LasiduDilshan/BMS_EDR_project/Solidworks/SW CONTROLLER/controller/Screenshot 2024-05-13 174024.png

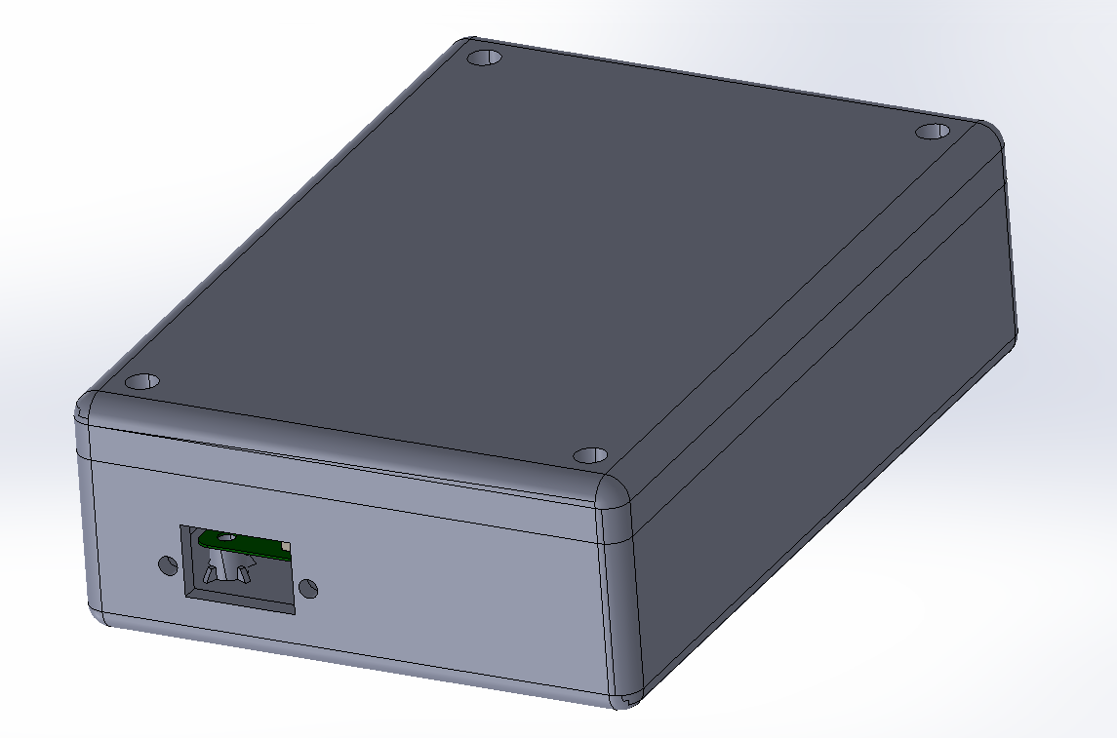
Solidworks/SW CONTROLLER/controller/Screenshot 2024-05-13 174024.png
