LasiduDilshan/BMS_EDR_project/Solidworks/SW CONTROLLER/controller/Screenshot 2024-05-13 174057.png

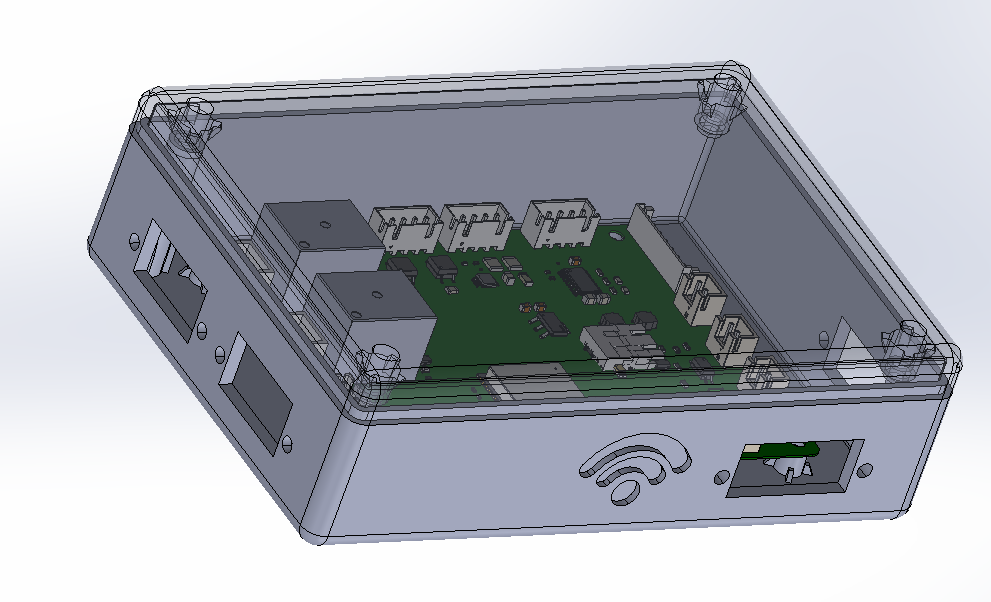
Solidworks/SW CONTROLLER/controller/Screenshot 2024-05-13 174057.png
