LasiduDilshan/BMS_EDR_project/Solidworks/SW CONTROLLER/controller/Screenshot 2024-05-13 174107.png

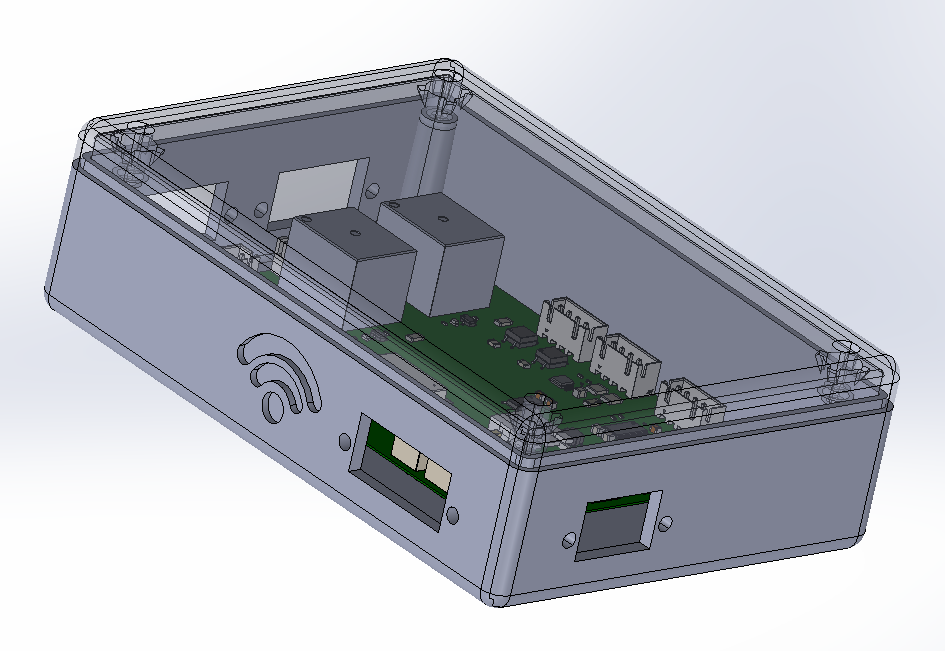
Solidworks/SW CONTROLLER/controller/Screenshot 2024-05-13 174107.png
