LasiduDilshan/BMS_EDR_project/Solidworks/SW/cell module/Screenshot 2024-05-13 142049.png

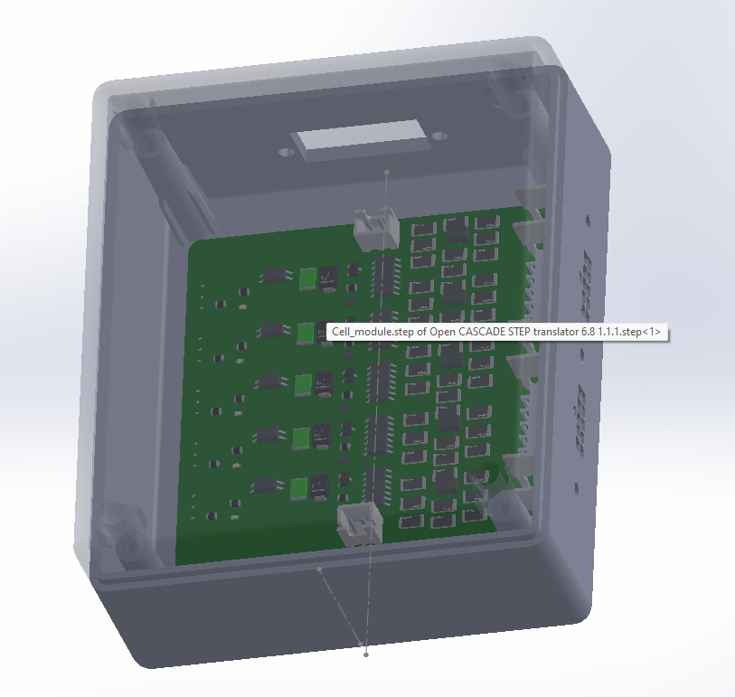
Solidworks/SW/cell module/Screenshot 2024-05-13 142049.png
