LasiduDilshan/BMS_EDR_project/PCBs/Cell Module/__Final cell module__/PCB with side mounts new.step

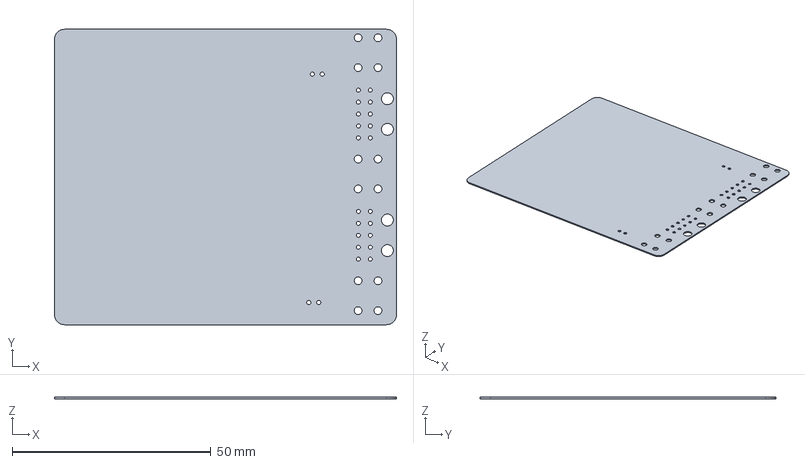
[picture p76: CAD file, 2024-07-03]
PCBs/Cell Module/__Final cell module__/PCB with side mounts new.step
86.0 x 74.3 x 0.411 mm
