LasiduDilshan/BMS_EDR_project/PCBs/Reference/BMS-Cell-Module-Circuit/DO-221AC.stp

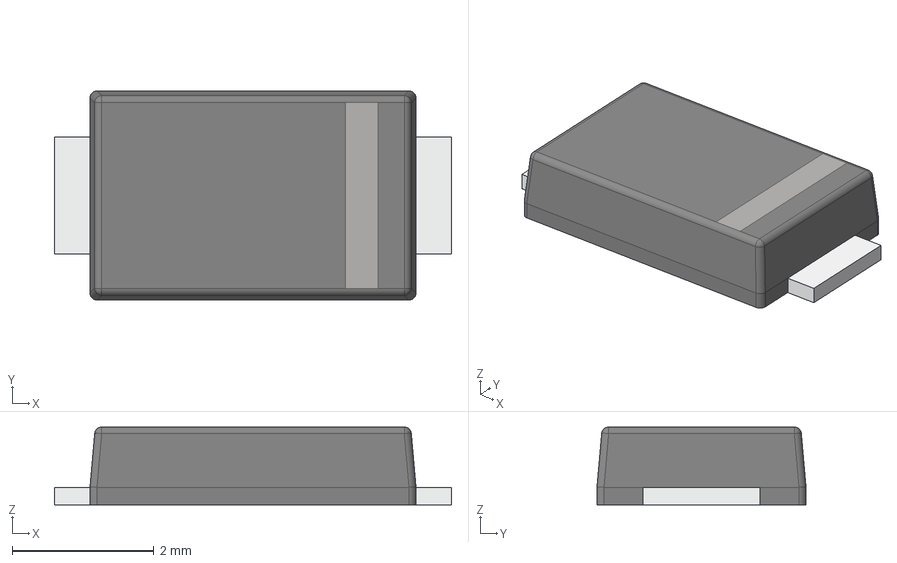
[picture p77: CAD file, 2024-07-03]
PCBs/Reference/BMS-Cell-Module-Circuit/DO-221AC.stp
5.60 x 2.95 x 1.10 mm
