LasiduDilshan/BMS_EDR_project/Solidworks/SW CONTROLLER/2nd below.SLDPRT

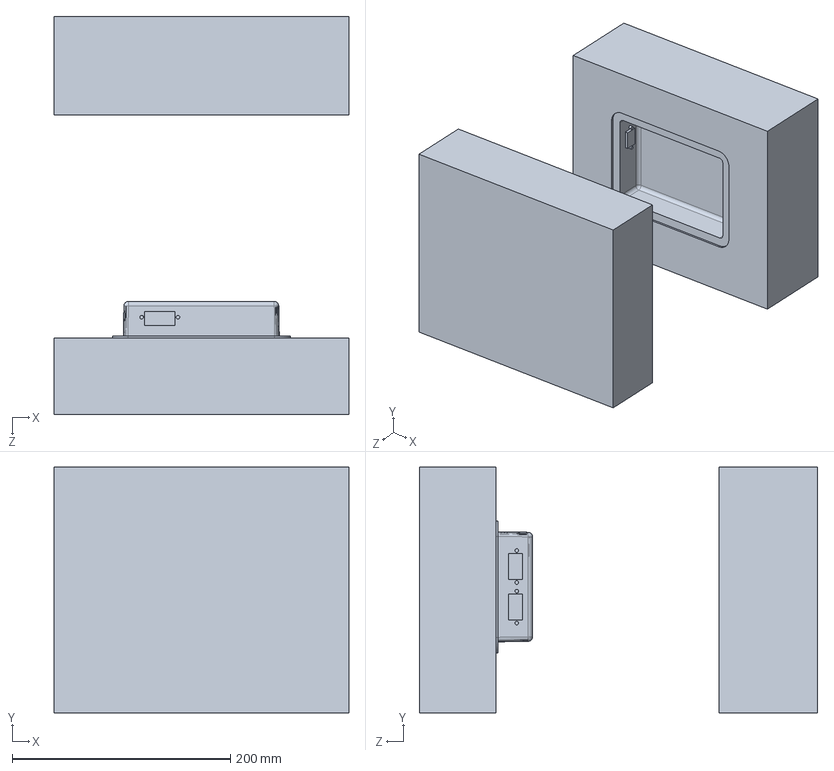
[picture p78: CAD file, 2024-10-22]
Solidworks/SW CONTROLLER/2nd below.SLDPRT
270.0 x 225.0 x 364.5 mm
