LasiduDilshan/BMS_EDR_project/Solidworks/SW CONTROLLER/MOLD/2nd below.SLDPRT

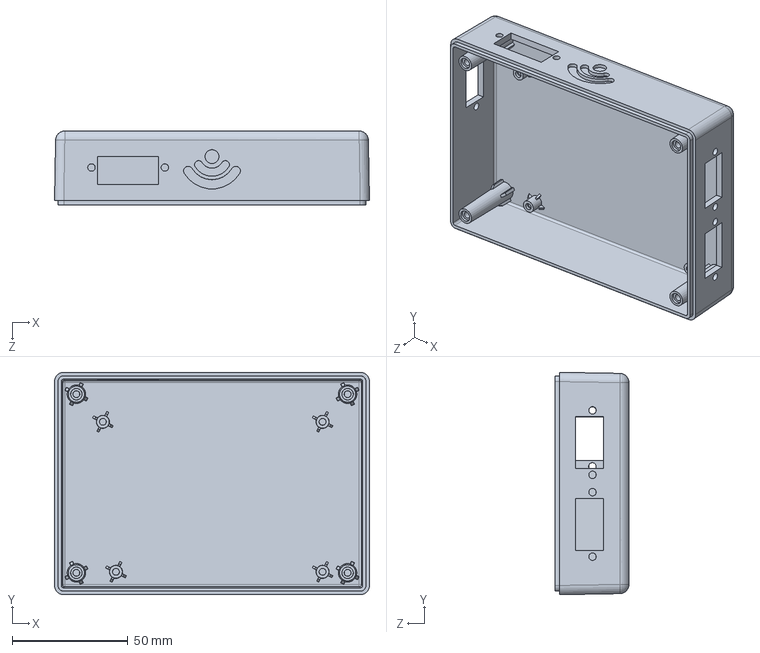
[picture p79: CAD file, 2024-10-22]
Solidworks/SW CONTROLLER/MOLD/2nd below.SLDPRT
136.0 x 96.0 x 32.0 mm
