LasiduDilshan/BMS_EDR_project/Solidworks/SW/MOLD/below part.SLDPRT

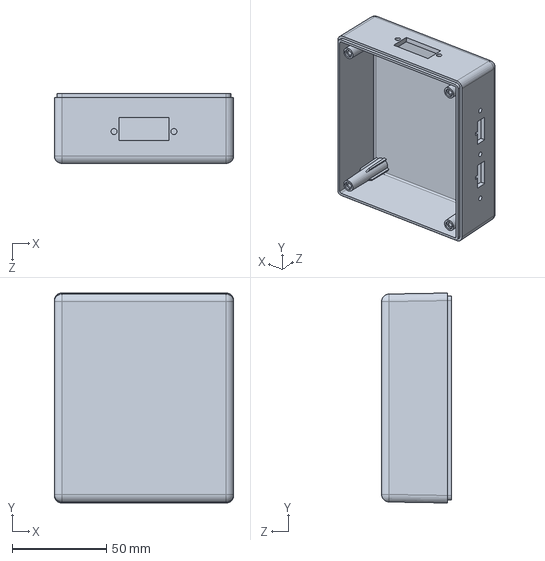
[picture p80: CAD file, 2024-10-22]
Solidworks/SW/MOLD/below part.SLDPRT
95.0 x 111.2 x 37.0 mm
