LasiduDilshan/BMS_EDR_project/Solidworks/SW/Top Part.SLDPRT

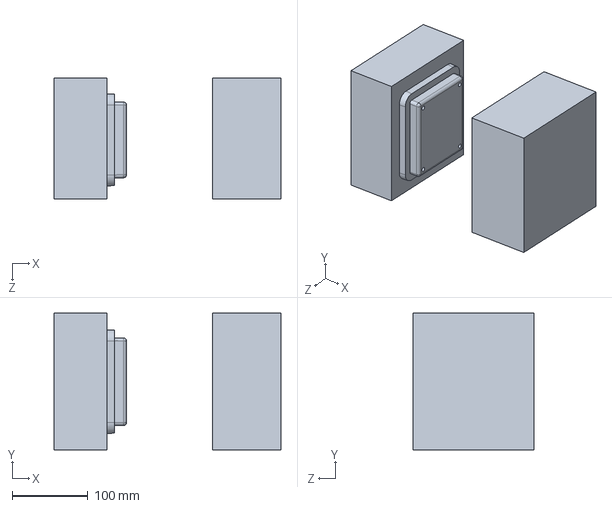
[picture p81: CAD file, 2024-10-22]
Solidworks/SW/Top Part.SLDPRT
299.0 x 180.0 x 160.0 mm
