LasiduDilshan/BMS_EDR_project/PCBs/Cell Module/__Final cell module__/PCB with side mounts.step

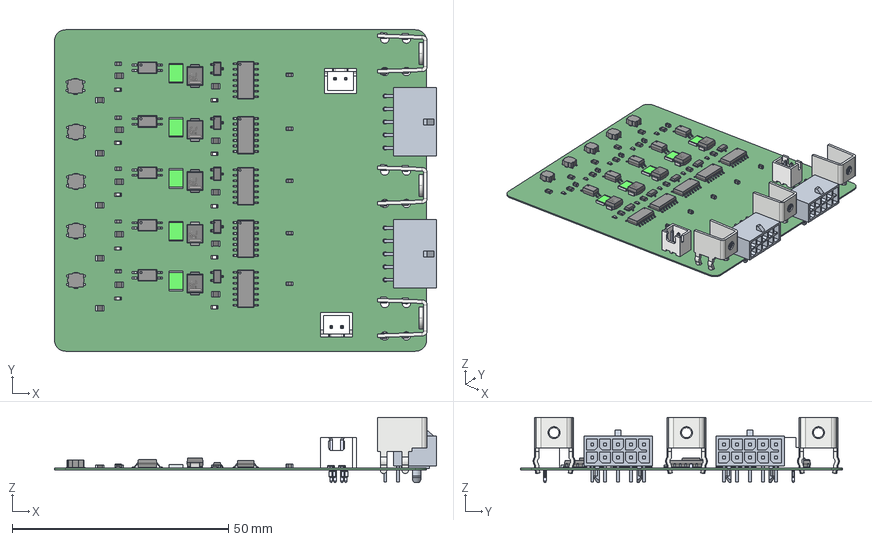
[picture p82: CAD file, 2024-07-03]
PCBs/Cell Module/__Final cell module__/PCB with side mounts.step
88.3 x 74.3 x 15.1 mm
Pins x 5
PinsArrayLR x 10
term1 x 20
term2 x 20
