LasiduDilshan/BMS_EDR_project/Solidworks/SW CONTROLLER/MOLD/2nd top.SLDPRT

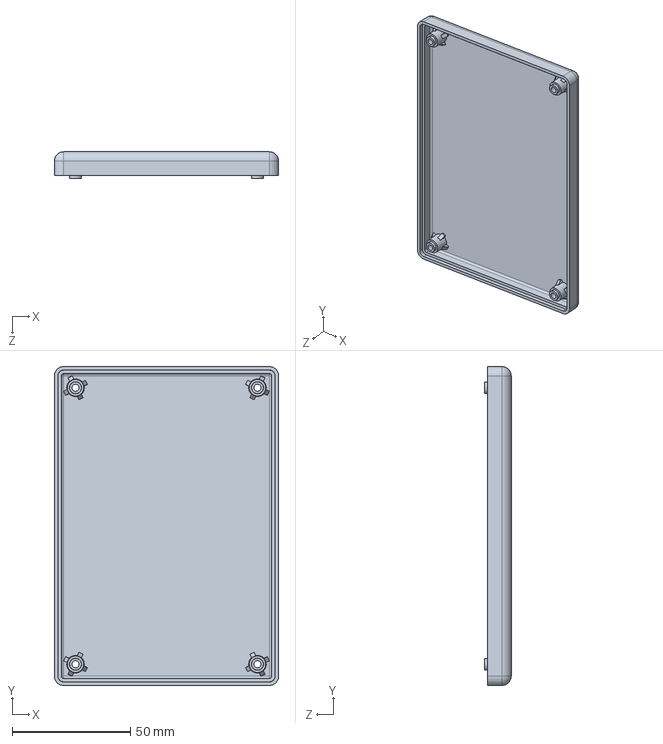
[picture p83: CAD file, 2024-10-22]
Solidworks/SW CONTROLLER/MOLD/2nd top.SLDPRT
95.0 x 135.0 x 11.2 mm
