LasiduDilshan/BMS_EDR_project/Solidworks/SW/below part.SLDPRT

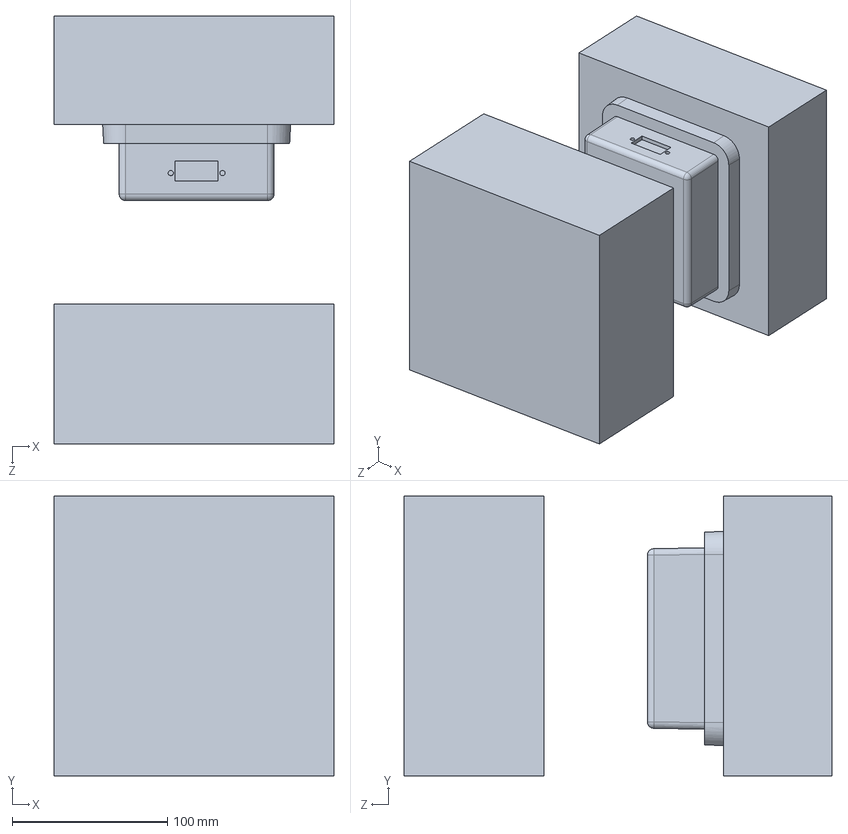
[picture p84: CAD file, 2024-10-22]
Solidworks/SW/below part.SLDPRT
180.0 x 180.0 x 275.5 mm
