LasiduDilshan/BMS_EDR_project/Solidworks/SW/MOLD/Top Part.SLDPRT

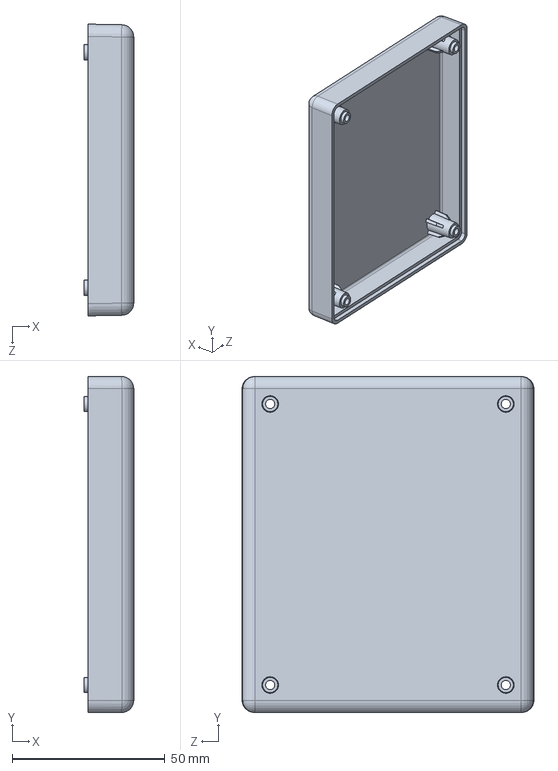
[picture p85: CAD file, 2024-10-22]
Solidworks/SW/MOLD/Top Part.SLDPRT
16.2 x 110.0 x 95.5 mm
