LasiduDilshan/BMS_EDR_project/PCBs/Cell Module/__Final cell module__/PCB2.step

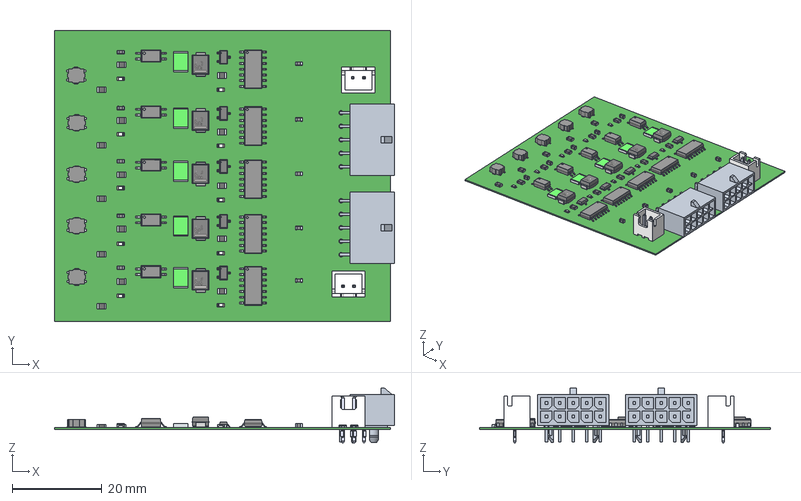
[picture p86: CAD file, 2024-07-03]
PCBs/Cell Module/__Final cell module__/PCB2.step
75.6 x 64.8 x 12.1 mm
Pins x 5
PinsArrayLR x 10
term1 x 20
term2 x 20
