LasiduDilshan/BMS_EDR_project/Solidworks/SW/Cell_module.step

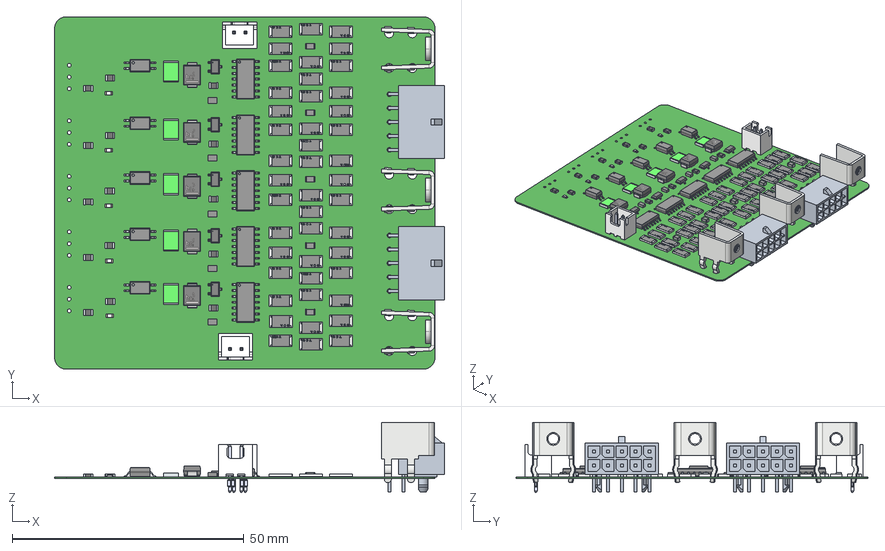
[picture p87: CAD file, 2024-10-22]
Solidworks/SW/Cell_module.step
84.2 x 76.1 x 15.1 mm
PinsArrayLR x 10
RC2010JK-071KL x 45
Yageo x 45
term1 x 25
term2 x 25
Pins x 5
