LasiduDilshan/BMS_EDR_project/Solidworks/SW CONTROLLER/2nd top.SLDPRT

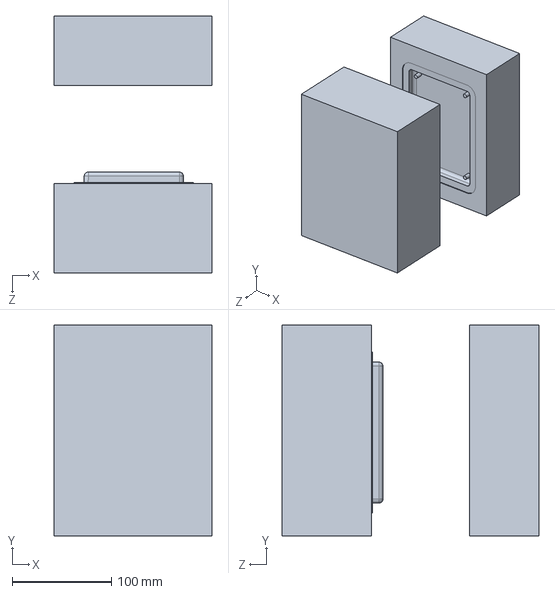
[picture p88: CAD file, 2024-10-22]
Solidworks/SW CONTROLLER/2nd top.SLDPRT
158.5 x 212.2 x 258.3 mm
