LasiduDilshan/BMS_EDR_project/Coding/Reduced Version/EBMS/ESPController/src/victron_canbus.cpp

/*
 ____  ____  _  _  ____  __  __  ___
(  _ \(_  _)( \/ )(  _ \(  \/  )/ __)
 )(_) )_)(_  \  /  ) _ < )    ( \__ \
(____/(____) (__) (____/(_/\/\_)(___/

(c) 2021-2023 Stuart Pittaway

This code communicates with VICTRON CERBO GX style devices using CANBUS @ 500kbps and 11 bit addresses.

The code supports the VICTRON CAN BUS BMS style messages.
*/

#define USE_ESP_IDF_LOG 1
static constexpr const char *const TAG = "Ebms-victron";

#include "victron_canbus.h"

// Transmit the EBMS hostname via two CAN Messages
void victron_message_370_371()
{
  char buffer[16+1];
  memset( buffer, 0, sizeof(buffer) );
  strncpy(buffer,hostname.c_str(),sizeof(buffer));

  send_canbus_message(0x370, (const uint8_t *)&buffer[0], 8);
  send_canbus_message(0x371, (const uint8_t *)&buffer[8], 8);
}

void victron_message_35e()
{
  send_canbus_message(0x35e, (const uint8_t*)hostname.c_str(), 6);
}

void victron_message_35f()
{
  struct data35f
  {
    // Not used
    uint16_t BatteryModel;
    uint16_t Firmwareversion;
    uint16_t OnlinecapacityinAh;
  };

  data35f data;

  // Not used by Victron
  data.BatteryModel = 0;
  // Need to swap bytes for this to make sense.
  data.Firmwareversion = ((uint16_t)COMPILE_WEEK_NUMBER_BYTE << 8) | COMPILE_YEAR_BYTE;

  data.OnlinecapacityinAh = mysettings.nominalbatcap;

  send_canbus_message(0x35f, (uint8_t *)&data, sizeof(data35f));
}

void SetBankAndModuleText(char *buffer, uint8_t cellid)
{
  uint8_t bank = cellid / mysettings.totalNumberOfSeriesModules;
  uint8_t module = cellid - (bank * mysettings.totalNumberOfSeriesModules);

  // Clear all 8 bytes
  memset(buffer, 0, 8);

  snprintf(buffer, 8, "b%d m%d", bank, module);
}

void victron_message_374_375_376_377()
{
  struct candata
  {
    char text[8];
  };

  candata data;

  if (rules.address_LowestCellVoltage < maximum_controller_cell_modules)
  {
    SetBankAndModuleText(data.text, rules.address_LowestCellVoltage);
    // Min. cell voltage id string [1]
    send_canbus_message(0x374, (uint8_t *)&data, sizeof(candata));
  }

  if (rules.address_HighestCellVoltage < maximum_controller_cell_modules)
  {
    SetBankAndModuleText(data.text, rules.address_HighestCellVoltage);
    // Max. cell voltage id string [1]
    send_canbus_message(0x375, (uint8_t *)&data, sizeof(candata));
  }

  if (rules.address_lowestExternalTemp < maximum_controller_cell_modules)
  {
    SetBankAndModuleText(data.text, rules.address_lowestExternalTemp);
    // Min. cell voltage id string [1]
    send_canbus_message(0x376, (uint8_t *)&data, sizeof(candata));
  }

  if (rules.address_highestExternalTemp < maximum_controller_cell_modules)
  {
    SetBankAndModuleText(data.text, rules.address_highestExternalTemp);
    // Min. cell voltage id string [1]
    send_canbus_message(0x377, (uint8_t *)&data, sizeof(candata));
  }
}

// CVL & CCL implementation
/*
At a fundamental level, Victron's approach to interacting with BMSes is in the form of 3 setpoint parameters:
* Charge Current Limit (CCL)
* Charge Voltage Limit (CVL)
* Discharge Current Limit (DCL)
Once the BMS is communicating with the GX device over CAN-bus, these parameters are listed in the "Parameters" menu in the battery device on the Remote Console.

All three parameter, but at least the CVL (Charge Voltage Limit) and CCL (Charge Current Limit), are sent by the BMS to the Victron system.
These are the only parameters that control the charging behaviour.

Victron's approach to BMSes and chargers is focused DC-Coupled solar systems where there can be multiple
charging sources, usually a combination of MPPT solar charger and charger/inverters.

AC-Coupled solar systems (non-Victron)

Typically, BMSes designed for the common AC-Coupled Energy Storage Type systems hardcode a
CVL, which remains the same in all situations. And will reduce CCL to 0, or near-zero, once the battery
is fully charged, and/or one of the cells is fully charged.
That strategy does not work with a Victron system.
*/
void victron_message_351()
{
  uint8_t number_of_active_errors = 0;

  struct data351
  {
    // CVL - 0.1V scale
    uint16_t chargevoltagelimit;
    // CCL - 0.1A scale
    int16_t maxchargecurrent;
    // DCL - 0.1A scale
    int16_t maxdischargecurrent;
    // Not currently used by Victron
    // 0.1V scale
    uint16_t dischargevoltage;
  };

  data351 data;

  // Defaults (do nothing)
  // Don't use zero for voltage - this indicates to Victron an over voltage situation, and Victron gear attempts to dump
  // the whole battery contents!  (feedback from end users)
  data.chargevoltagelimit = rules.lowestBankVoltage / 100;
  data.maxchargecurrent = 0;

  if (rules.IsChargeAllowed(&mysettings))
  {
    if (rules.numberOfBalancingModules > 0 && mysettings.stopchargebalance == true)
    {
      // Balancing, stop charge
      data.chargevoltagelimit = rules.lowestBankVoltage / 100;
      data.maxchargecurrent = 0;
    }
    else
    {
      // Default - normal behaviour
      data.chargevoltagelimit = rules.DynamicChargeVoltage();
      data.maxchargecurrent = rules.DynamicChargeCurrent();
    }
  }

  // Discharge settings....
  data.maxdischargecurrent = 0;
  data.dischargevoltage = mysettings.dischargevolt;

  if (rules.IsDischargeAllowed(&mysettings))
  {
    data.maxdischargecurrent = mysettings.dischargecurrent;
  }

  send_canbus_message(0x351, (uint8_t *)&data, sizeof(data351));
}

// S.o.C value
void victron_message_355()
{
  struct data355
  {
    uint16_t stateofchargevalue;
    // uint16_t stateofhealthvalue;
    // uint16_t highresolutionsoc;
  };

  if (_controller_state == ControllerState::Running && mysettings.currentMonitoringEnabled && currentMonitor.validReadings && (mysettings.currentMonitoringDevice == CurrentMonitorDevice::EBMS_CURRENT_MON_MODBUS || mysettings.currentMonitoringDevice == CurrentMonitorDevice::EBMS_CURRENT_MON_INTERNAL))
  {
    data355 data;
    // 0 SOC value un16 1 %
    data.stateofchargevalue = rules.StateOfChargeWithRulesApplied(&mysettings, currentMonitor.stateofcharge);
    // 2 SOH value un16 1 %
    // data.stateofhealthvalue = 100;

    send_canbus_message(0x355, (uint8_t *)&data, sizeof(data355));
  }
}

// Battery voltage
void victron_message_356()
{
  struct data356
  {
    int16_t voltage;
    int16_t current;
    int16_t temperature;
  };

  data356 data;

  // Use highest bank voltage calculated by controller and modules
  // Scale 0.01V
  data.voltage = rules.highestBankVoltage / 10;

  // If current shunt is installed, use the voltage from that as it should be more accurate
  if (mysettings.currentMonitoringEnabled && currentMonitor.validReadings)
  {
    data.voltage = currentMonitor.modbus.voltage * 100.0;
  }

  data.current = 0;
  // If current shunt is installed, use it
  if (mysettings.currentMonitoringEnabled && currentMonitor.validReadings)
  {
    // Scale 0.1A
    data.current = currentMonitor.modbus.current * 10;
  }

  // Temperature 0.1C using external temperature sensor
  if (rules.moduleHasExternalTempSensor)
  {
    data.temperature = (int16_t)rules.highestExternalTemp * (int16_t)10;
  }
  else
  {
    // No external temp sensors
    data.temperature = 0;
  }

  send_canbus_message(0x356, (uint8_t *)&data, sizeof(data356));
}

// Send alarm details to Victron over CANBUS
void victron_message_35a()
{

  struct data35a
  {
    uint8_t byte0;
    uint8_t byte1;
    uint8_t byte2;
    uint8_t byte3;
    uint8_t byte4;
    uint8_t byte5;
    uint8_t byte6;
    uint8_t byte7;
  };

  data35a data;

  memset(&data, 0, sizeof(data35a));

  // B00 = Alarm not supported
  // B10 = Alarm/warning active
  // B01 = Alarm/warning inactive (status = OK)

  // These constants are actually bit swapped compared to the notes above
  // as the Victron kit uses little-endian ordering when transmitting on CANBUS
  const uint8_t BIT01_ALARM = B00000001;
  const uint8_t BIT23_ALARM = B00000100;
  const uint8_t BIT45_ALARM = B00010000;
  const uint8_t BIT67_ALARM = B01000000;

  const uint8_t BIT01_OK = B00000010;
  const uint8_t BIT23_OK = B00001000;
  const uint8_t BIT45_OK = B00100000;
  const uint8_t BIT67_OK = B10000000;

  // const uint8_t BIT01_NOTSUP = B00000011;
  // const uint8_t BIT23_NOTSUP = B00001100;
  // const uint8_t BIT45_NOTSUP = B00110000;
  // const uint8_t BIT67_NOTSUP = B11000000;

  if (_controller_state == ControllerState::Running)
  {
    // BYTE 0
    //(bit 0+1) General alarm (not implemented)
    //(bit 2+3) Battery low voltage alarm
    data.byte0 |= ((rules.ruleOutcome(Rule::BankOverVoltage) | rules.ruleOutcome(Rule::CurrentMonitorOverVoltage)) ? BIT23_ALARM : BIT23_OK);
    //(bit 4+5) Battery high voltage alarm
    data.byte0 |= ((rules.ruleOutcome(Rule::BankUnderVoltage) | rules.ruleOutcome(Rule::CurrentMonitorUnderVoltage)) ? BIT45_ALARM : BIT45_OK);

    //(bit 6+7) Battery high temperature alarm
    if (rules.moduleHasExternalTempSensor)
    {
      data.byte0 |= (rules.ruleOutcome(Rule::ModuleOverTemperatureExternal) ? BIT67_ALARM : BIT67_OK);
    }

    // BYTE 1
    // 1 (bit 0+1) Battery low temperature alarm
    if (rules.moduleHasExternalTempSensor)
    {
      data.byte1 |= (rules.ruleOutcome(Rule::ModuleUnderTemperatureExternal) ? BIT01_ALARM : BIT01_OK);
    }
    // 1 (bit 2+3) Battery high temperature charge alarm
    // data.byte1 |= BIT23_NOTSUP;
    // 1 (bit 4+5) Battery low temperature charge alarm
    // data.byte1 |= BIT45_NOTSUP;
    // 1 (bit 6+7) Battery high current alarm
    // data.byte1 |= BIT67_NOTSUP;
  }

  // 2 (bit 0+1) Battery high charge current alarm
  // data.byte2 |= BIT01_NOTSUP;
  // 2 (bit 2+3) Contactor Alarm (not implemented)
  // data.byte2 |= BIT23_NOTSUP;
  // 2 (bit 4+5) Short circuit Alarm (not implemented)
  // data.byte2 |= BIT45_NOTSUP;

  // 2 (bit 6+7) BMS internal alarm
  data.byte2 |= ((rules.ruleOutcome(Rule::BMSError) || rules.ruleOutcome(Rule::EmergencyStop)) ? BIT67_ALARM : BIT67_OK);

  // 3 (bit 0+1) Cell imbalance alarm
  // data.byte3 |= BIT01_NOTSUP;
  // 3 (bit 2+3) Reserved
  // 3 (bit 4+5) Reserved
  // 3 (bit 6+7) Reserved

  // 4 (bit 0+1) General warning (not implemented)
  // data.byte4 |= BIT01_NOTSUP;
  // 4 (bit 2+3) Battery low voltage warning
  // data.byte4 |= BIT23_NOTSUP;
  // 4 (bit 4+5) Battery high voltage warning
  // data.byte4 |= BIT45_NOTSUP;
  // 4 (bit 6+7) Battery high temperature warning
  // data.byte4 |= BIT67_NOTSUP;

  // 5 (bit 0+1) Battery low temperature warning
  // data.byte5 |= BIT01_NOTSUP;
  // 5 (bit 2+3) Battery high temperature charge warning
  // data.byte5 |= BIT23_NOTSUP;
  // 5 (bit 4+5) Battery low temperature charge warning
  // data.byte5 |= BIT45_NOTSUP;
  // 5 (bit 6+7) Battery high current warning
  // data.byte5 |= BIT67_NOTSUP;

  // 6 (bit 0+1) Battery high charge current warning
  // data.byte6 |= BIT01_NOTSUP;
  // 6 (bit 2+3) Contactor warning (not implemented)
  // data.byte6 |= BIT23_NOTSUP;
  // 6 (bit 4+5) Short circuit warning (not implemented)
  // data.byte6 |= BIT45_NOTSUP;
  // 6 (bit 6+7) BMS internal warning
  // data.byte6 |= (rules.numberOfActiveWarnings > 0 ? BIT67_ALARM : BIT67_OK);

  // ESP_LOGI(TAG, "numberOfBalancingModules=%u", rules.numberOfBalancingModules);

  // 7 (bit 0+1) Cell imbalance warning
  // data.byte7 |= (rules.numberOfBalancingModules > 0 ? BIT01_ALARM : BIT01_OK);
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
